mausi-mick/KS_ESP32/ESP32_R.pdf

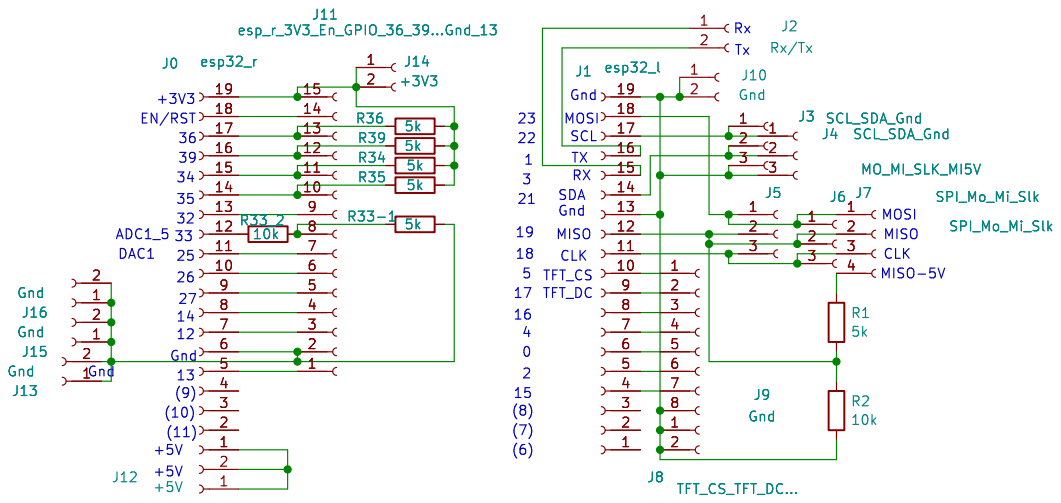
[picture p2: page 1]

Id: 1/1 Title: File: ESP32_R.kicad_sch Sheet: /
