mausi-mick/KS_ESP32/ESP32_R-F_Silkscreen.pdf

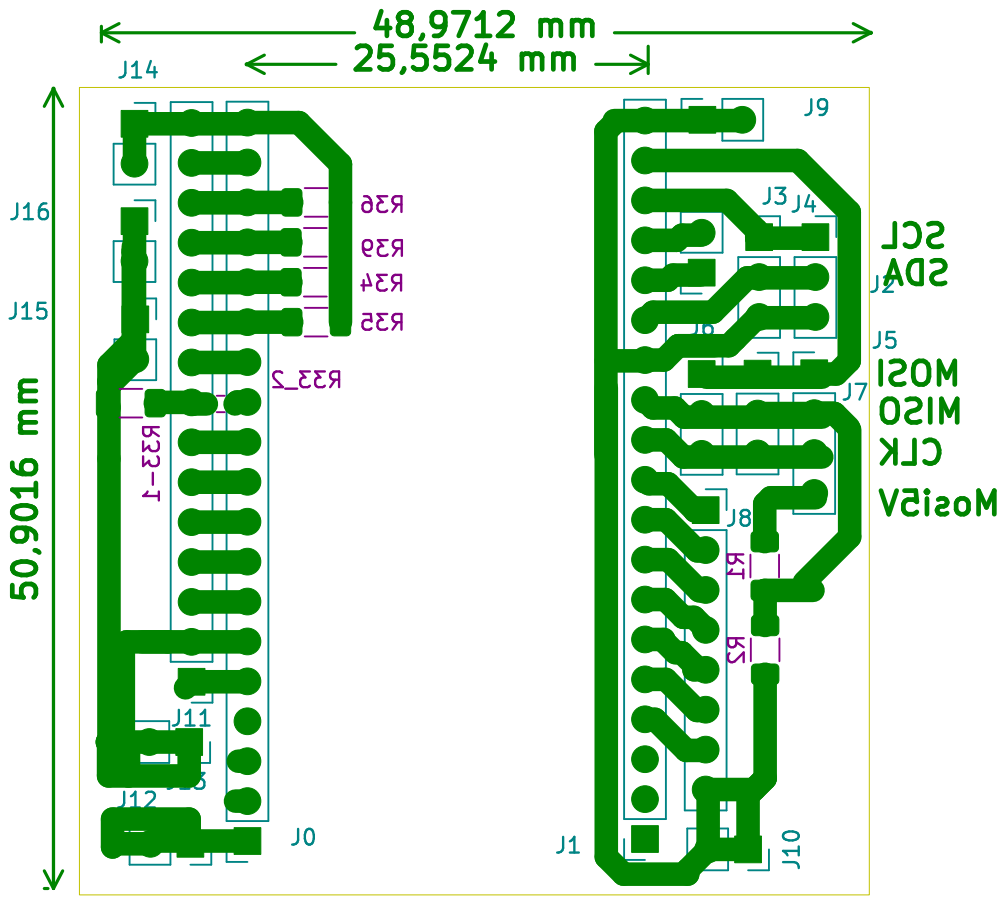
[picture p9: page 1]
