mausi-mick/KS_ESP32/FreeSerif9pt7b.h

const uint8_t FreeSerif9pt7b[] PROGMEM = {
  0xFF, 0xEA, 0x03, 0xDE, 0xF7, 0x20, 0x11, 0x09, 0x04, 0x82, 0x4F, 0xF9,
  0x10, 0x89, 0xFF, 0x24, 0x12, 0x09, 0x0C, 0x80, 0x10, 0x7C, 0xD6, 0xD2,
  0xD0, 0xF0, 0x38, 0x1E, 0x17, 0x93, 0x93, 0xD6, 0x7C, 0x10, 0x38, 0x43,
  0x3C, 0x39, 0x21, 0x8A, 0x0C, 0x50, 0x65, 0x39, 0xCB, 0x20, 0xB9, 0x05,
  0x88, 0x4C, 0x44, 0x64, 0x21, 0xC0, 0x0E, 0x00, 0xC8, 0x06, 0x40, 0x32,
  0x01, 0xA0, 0x07, 0x78, 0x31, 0x87, 0x88, 0x46, 0x86, 0x34, 0x30, 0xC1,
  0xC7, 0x17, 0xCF, 0x00, 0xFE, 0x08, 0x88, 0x84, 0x63, 0x18, 0xC6, 0x10,
  0x82, 0x08, 0x20, 0x82, 0x08, 0x21, 0x0C, 0x63, 0x18, 0xC4, 0x22, 0x22,
  0x00, 0x63, 0x9A, 0xDC, 0x72, 0xB6, 0x08, 0x08, 0x04, 0x02, 0x01, 0x0F,
  0xF8, 0x40, 0x20, 0x10, 0x08, 0x00, 0xD8, 0xF0, 0xF0, 0x08, 0x84, 0x22,
  0x10, 0x8C, 0x42, 0x31, 0x00, 0x1C, 0x31, 0x98, 0xD8, 0x3C, 0x1E, 0x0F,
  0x07, 0x83, 0xC1, 0xE0, 0xD8, 0xC4, 0x61, 0xC0, 0x13, 0x8C, 0x63, 0x18,
  0xC6, 0x31, 0x8C, 0x67, 0x80, 0x3C, 0x4E, 0x86, 0x06, 0x06, 0x04, 0x0C,
  0x08, 0x10, 0x20, 0x41, 0xFE, 0x3C, 0xC6, 0x06, 0x04, 0x1C, 0x3E, 0x07,
  0x03, 0x03, 0x03, 0x06, 0xF8, 0x04, 0x18, 0x71, 0x64, 0xC9, 0xA3, 0x46,
  0xFE, 0x18, 0x30, 0x60, 0x0F, 0x10, 0x20, 0x3C, 0x0E, 0x07, 0x03, 0x03,
  0x03, 0x02, 0x04, 0xF8, 0x07, 0x1C, 0x30, 0x60, 0x60, 0xDC, 0xE6, 0xC3,
  0xC3, 0xC3, 0x43, 0x66, 0x3C, 0x7F, 0x82, 0x02, 0x02, 0x04, 0x04, 0x04,
  0x08, 0x08, 0x08, 0x10, 0x10, 0x3C, 0x8F, 0x1E, 0x3E, 0x4F, 0x06, 0x36,
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
  {   401,   9,  12,  10,    1,  -11 },   // 0x46 'F'
  {   415,  12,  12,  13,    1,  -11 },   // 0x47 'G'
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

const GFXfont FreeSerif9pt7b PROGMEM = {
  (uint8_t  *)FreeSerif9pt7bBitmaps,
  (GFXglyph *)FreeSerif9pt7bGlyphs,
  0x20, 0x7E, 22 };

// Approx. 1752 bytes
